luftaquila/hardware-meter/src-tauri/src/common.rs

use std::{
    fs,
    io::{Error, Write},
    path::PathBuf,
};

use directories::ProjectDirs;
use serde::{Deserialize, Serialize};
use strum_macros::{AsRefStr, EnumIter, EnumMessage};

pub const MAX_CHANNEL: i32 = 6;

#[derive(Clone, Copy, Default, AsRefStr, EnumIter, EnumMessage, Serialize, Deserialize, Debug)]
pub enum NetworkSpeed {
    #[strum(detailed_message = "1 Mbps")]
    Mbps1 = 1,
    #[strum(detailed_message = "5 Mbps")]
    Mbps5 = 5,
    #[strum(detailed_message = "10 Mbps")]
    Mbps10 = 10,
    #[strum(detailed_message = "50 Mbps")]
    Mbps50 = 50,
    #[default]
    #[strum(detailed_message = "100 Mbps")]
    Mbps100 = 100,
    #[strum(detailed_message = "500 Mbps")]
    Mbps500 = 500,
    #[strum(detailed_message = "1 Gbps")]
    Gbps1 = 1000,
    #[strum(detailed_message = "5 Gbps")]
    Gbps5 = 5000,
}

#[derive(AsRefStr, EnumIter, EnumMessage, Serialize, Deserialize, Debug)]
pub enum Gauge {
    #[strum(detailed_message = "Disabled")]
    Disabled,

    #[strum(detailed_message = "CPU Utilization")]
    CpuUsage { core: i32 },
    #[strum(detailed_message = "CPU Frequency")]
    CpuFreq { core: i32 },
    #[strum(detailed_message = "CPU Temperature")]
    CpuTemp,

    #[strum(detailed_message = "Memory Usage")]
    MemoryUsage,
    #[strum(detailed_message = "Swap Usage")]
    SwapUsage,

    #[strum(detailed_message = "Network Transmit Speed")]
    NetTx { netif: String, unit: NetworkSpeed },
    #[strum(detailed_message = "Network Receive Speed")]
    NetRx { netif: String, unit: NetworkSpeed },
    #[strum(detailed_message = "Network Receive & Transmit Speed")]
    NetTxRx { netif: String, unit: NetworkSpeed },

    #[strum(detailed_message = "Disk Usage")]
    DiskUsage { name: String },
    #[strum(detailed_message = "Disk Write Speed")]
    DiskTx { name: String },
    #[strum(detailed_message = "Disk Read Speed")]
    DiskRx { name: String },
    #[strum(detailed_message = "Disk Read & Write Speed")]
    DiskTxRx { name: String },

    #[strum(detailed_message = "GPU Utilization")]
    GpuUsage { id: i32 },
    #[strum(detailed_message = "GPU Core Frequency")]
    GpuFreq { id: i32 },
    #[strum(detailed_message = "GPU Temperature")]
    GpuTemp { id: i32 },
}

#[derive(Serialize, Deserialize, Debug)]
pub struct ConfigFile {
    pub power: bool,
    pub port: String,
    pub update: u64,
    pub gauges: Vec<Gauge>,
}

impl ConfigFile {
    pub fn to_json(&self) -> Result<(), Error> {
        let mut file = fs::File::create(ConfigFile::path())?;

        let serialized = serde_json::to_string_pretty(self)?;
        file.write_all(serialized.as_bytes())?;

        Ok(())
    }

    pub fn from_json() -> Result<ConfigFile, Error> {
        let json = fs::read_to_string(ConfigFile::path())?;

        Ok(serde_json::from_str(&json)?)
    }

    pub fn path() -> PathBuf {
        ProjectDirs::from("", "luftaquila", "hardware-meter")
            .unwrap()
            .data_local_dir()
            .to_path_buf()
            .join("config.json")
    }

    pub fn dir() -> PathBuf {
        ProjectDirs::from("", "luftaquila", "hardware-meter")
            .unwrap()
            .data_local_dir()
            .to_path_buf()
    }
}

pub fn min_f32(x: f32, y: f32) -> f32 {
    if x < y {
        x
    } else {
        y
    }
}
